gvJaime/microspot/Mechanical/Step/Printed/Axes/YCarriage/LYCarriage.step

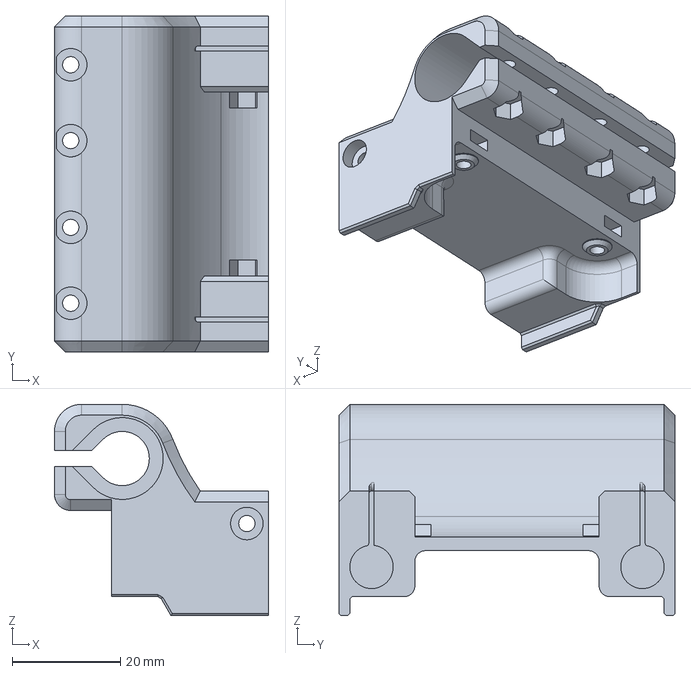
[picture p22: CAD file, 2017-04-26]
Mechanical/Step/Printed/Axes/YCarriage/LYCarriage.step
39.5 x 62.0 x 39.0 mm
