gvJaime/microspot/Mechanical/Step/Printed/Axes/ZAxis/BackCraneGuide.step

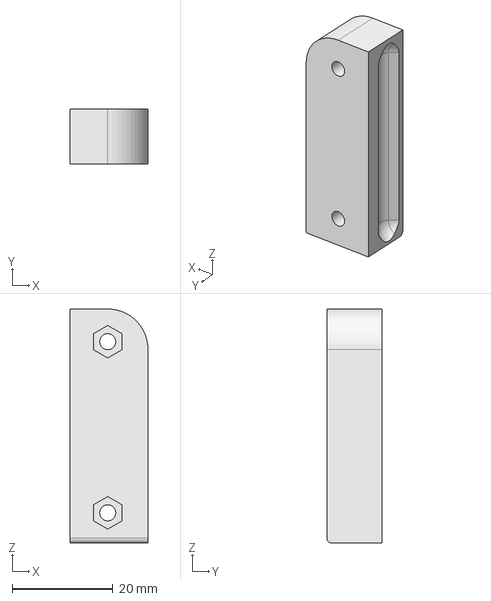
[picture p23: CAD file, 2018-11-02]
Mechanical/Step/Printed/Axes/ZAxis/BackCraneGuide.step
15.5 x 11.0 x 46.5 mm
