gvJaime/microspot/Mechanical/Step/Printed/Electronics Holder/ElecBase.step

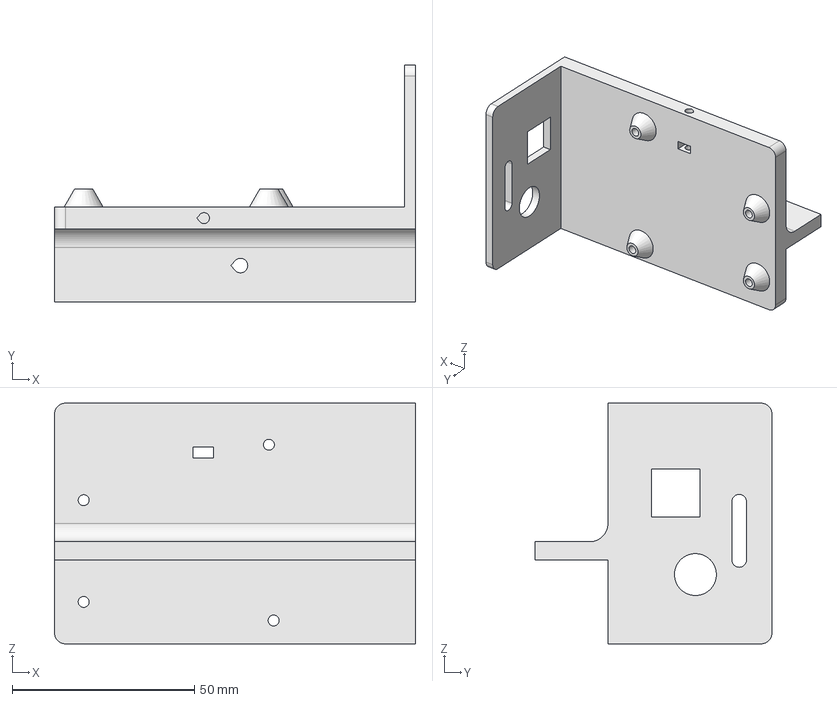
[picture p24: CAD file, 2016-09-07]
Mechanical/Step/Printed/Electronics Holder/ElecBase.step
99.0 x 65.0 x 66.0 mm
