gvJaime/microspot/Mechanical/Step/Printed/MainFrame/LAxisShield.step

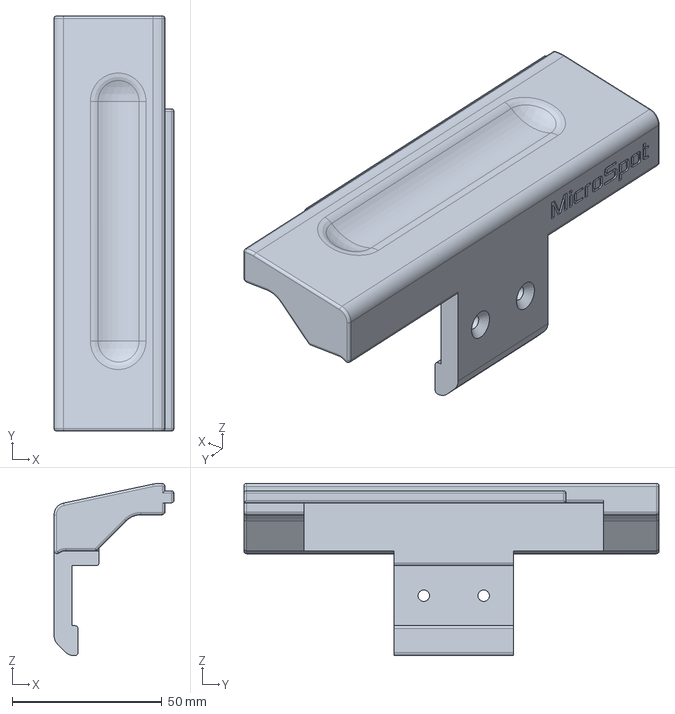
[picture p25: CAD file, 2018-11-02]
Mechanical/Step/Printed/MainFrame/LAxisShield.step
40.0 x 138.5 x 57.5 mm
