gvJaime/microspot/Mechanical/Step/Printed/PhoneHolder/Ratchet.step

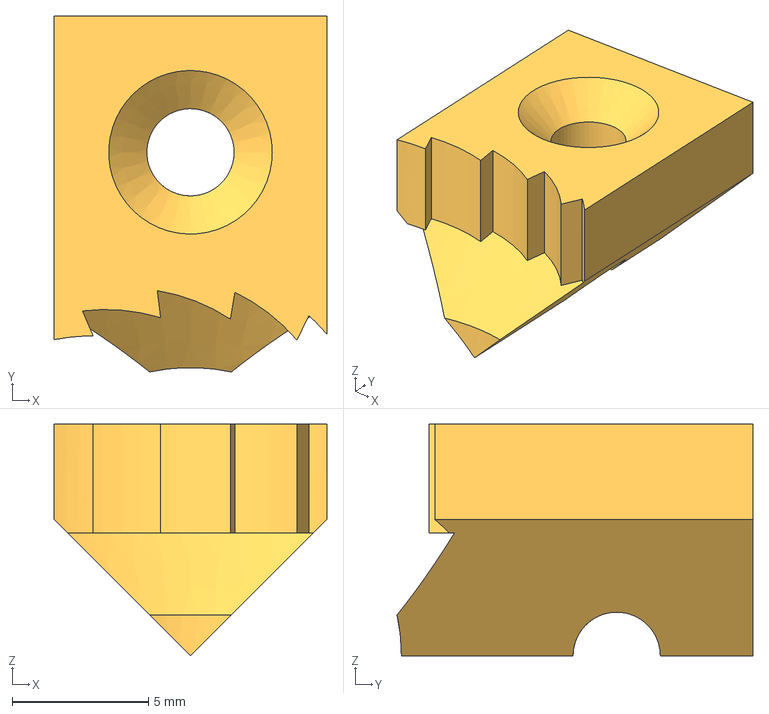
[picture p26: CAD file, 2018-11-02]
Mechanical/Step/Printed/PhoneHolder/Ratchet.step
10.0 x 13.1 x 8.50 mm
