gvJaime/microspot/Mechanical/Step/Printed/SmartphoneHolder/LPhoneGrip.step

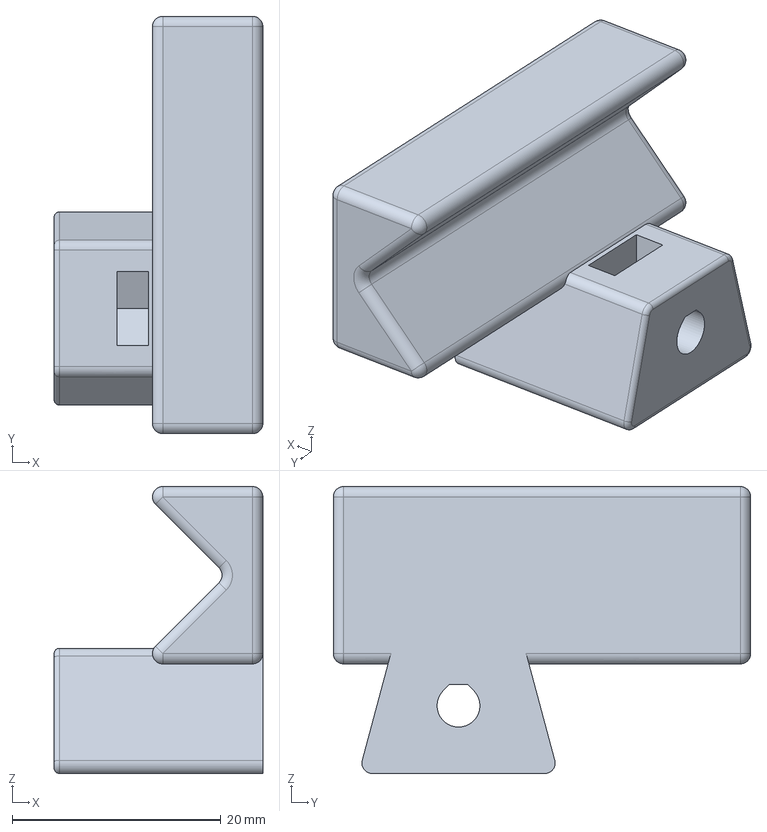
[picture p27: CAD file, 2017-04-26]
Mechanical/Step/Printed/SmartphoneHolder/LPhoneGrip.step
20.0 x 40.0 x 27.5 mm
