gvJaime/microspot/Optical/KO_LA0704/Lid.step

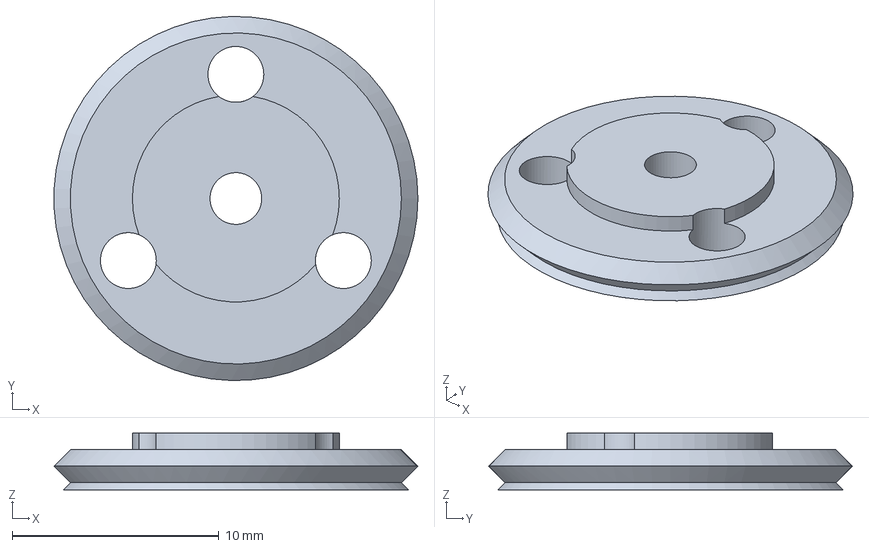
[picture p28: CAD file, 2018-11-02]
Optical/KO_LA0704/Lid.step
17.6 x 17.6 x 2.75 mm
