gvJaime/microspot/Optical/KO_LAQ0202nLAP0617/Lower.step

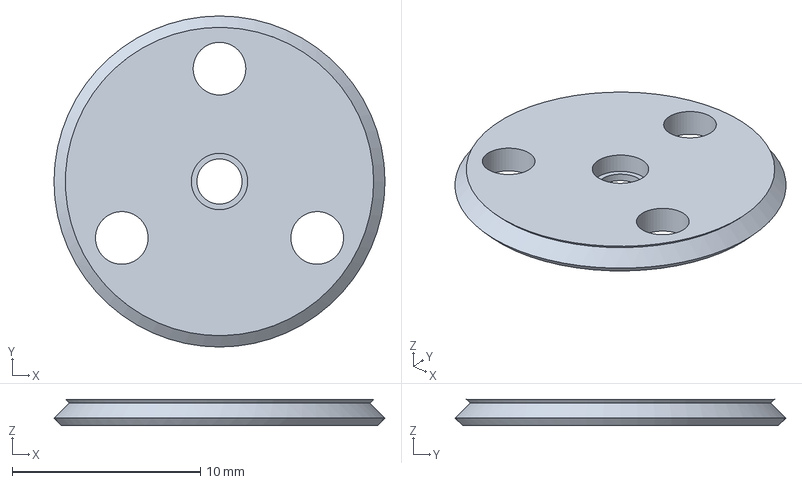
[picture p29: CAD file, 2018-11-02]
Optical/KO_LAQ0202nLAP0617/Lower.step
17.6 x 17.6 x 1.40 mm
