gvJaime/microspot/Optical/LensMount/LensFixTemplate.fcstd

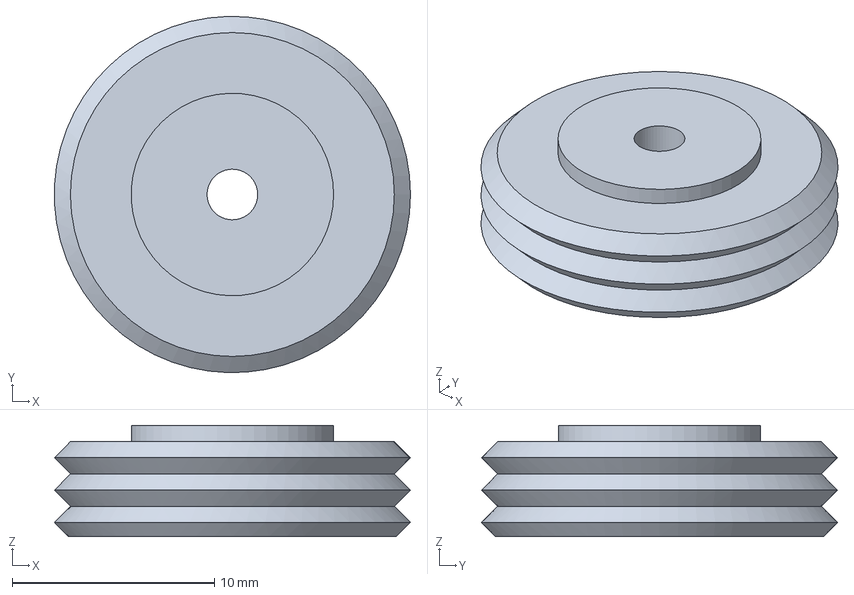
[picture p30: CAD file, 2018-11-02]
Optical/LensMount/LensFixTemplate.fcstd
17.6 x 17.6 x 5.50 mm
