gvJaime/microspot/Tools/NEMAChanger.fcstd

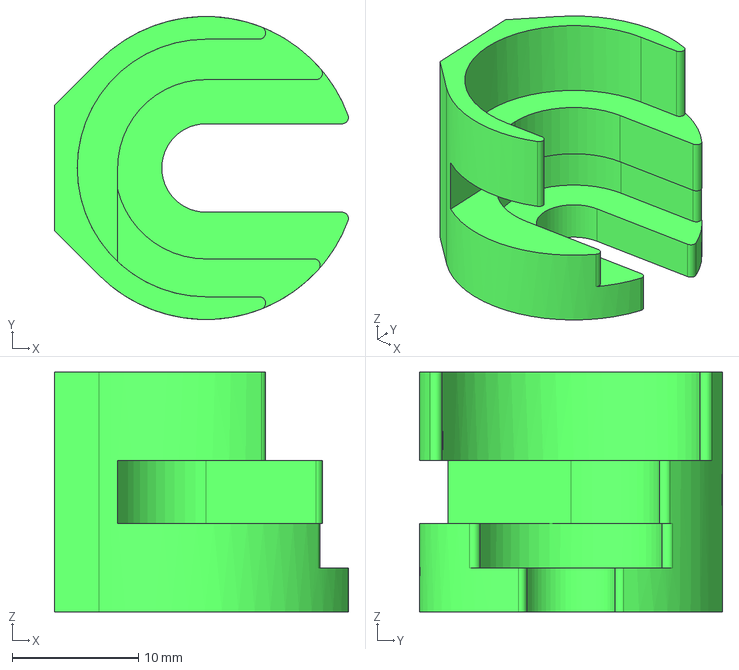
[picture p31: CAD file, 2018-11-02]
Tools/NEMAChanger.fcstd
23.3 x 24.0 x 19.0 mm
