gvJaime/microspot/Mechanical/src/Axes/XCarriage/FastRead102/FastReadFix.fcstd

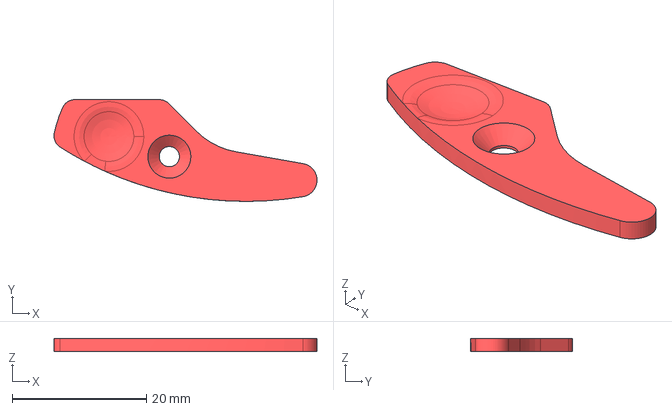
[picture p32: CAD file, 2017-07-26]
Mechanical/src/Axes/XCarriage/FastRead102/FastReadFix.fcstd
39.2 x 15.2 x 2.00 mm
