gvJaime/microspot/Mechanical/src/Axes/XCarriage/Neubauer/NeubauerTop.fcstd

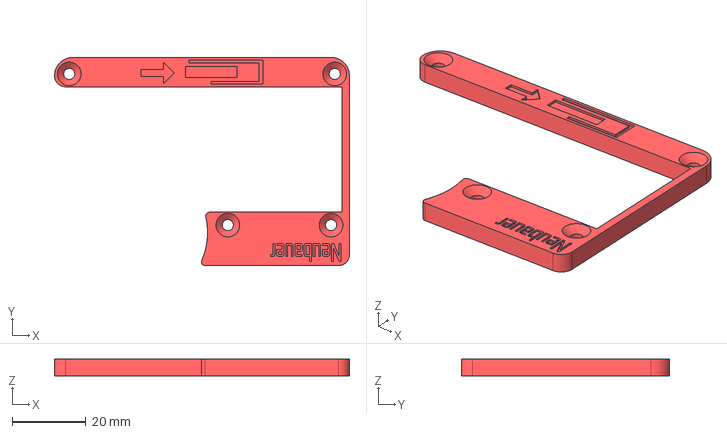
[picture p33: CAD file, 2018-11-02]
Mechanical/src/Axes/XCarriage/Neubauer/NeubauerTop.fcstd
80.0 x 56.5 x 4.50 mm
