gvJaime/microspot/Mechanical/src/Axes/XCarriage/StdTray/StdTop.fcstd

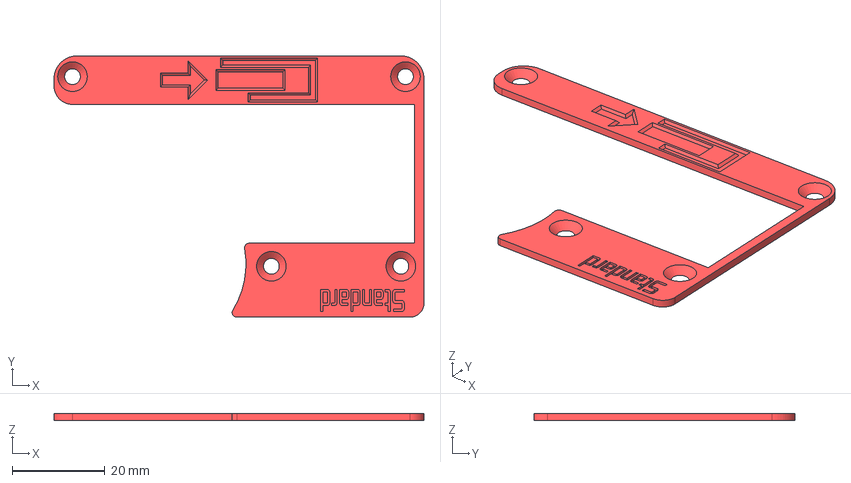
[picture p34: CAD file, 2018-11-02]
Mechanical/src/Axes/XCarriage/StdTray/StdTop.fcstd
80.0 x 56.5 x 1.50 mm
