gvJaime/microspot/Mechanical/src/Axes/XCarriage/Xcarriage.fcstd

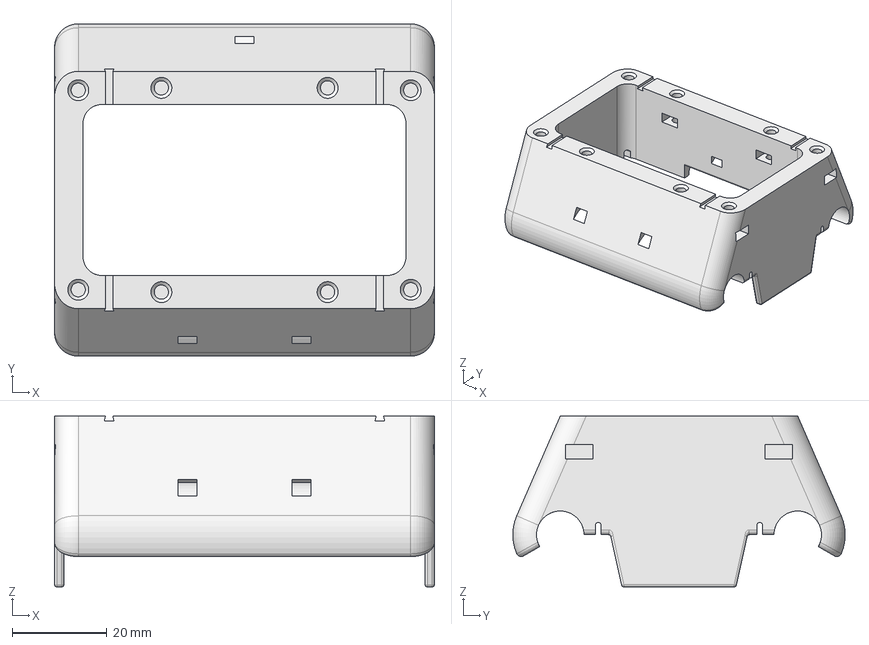
[picture p35: CAD file, 2016-09-07]
Mechanical/src/Axes/XCarriage/Xcarriage.fcstd
80.0 x 70.0 x 36.0 mm
