gvJaime/microspot/Mechanical/src/Axes/YCarriage/MiniIdler.fcstd

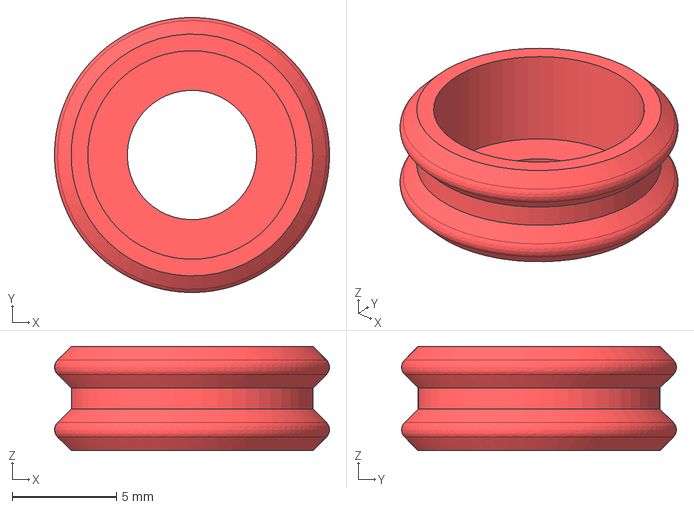
[picture p36: CAD file, 2016-04-19]
Mechanical/src/Axes/YCarriage/MiniIdler.fcstd
13.2 x 13.2 x 5.00 mm
