gvJaime/microspot/Mechanical/src/Axes/ZCarriage/FrontGuide.fcstd

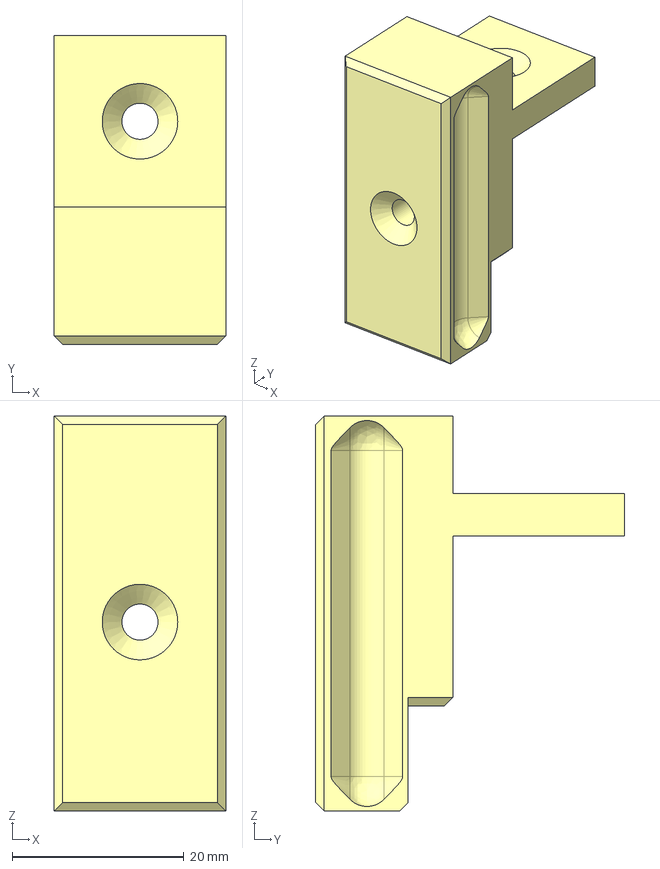
[picture p37: CAD file, 2018-11-02]
Mechanical/src/Axes/ZCarriage/FrontGuide.fcstd
20.0 x 36.0 x 46.0 mm
