gvJaime/microspot/Mechanical/src/MainFrame/FrontCorner.fcstd

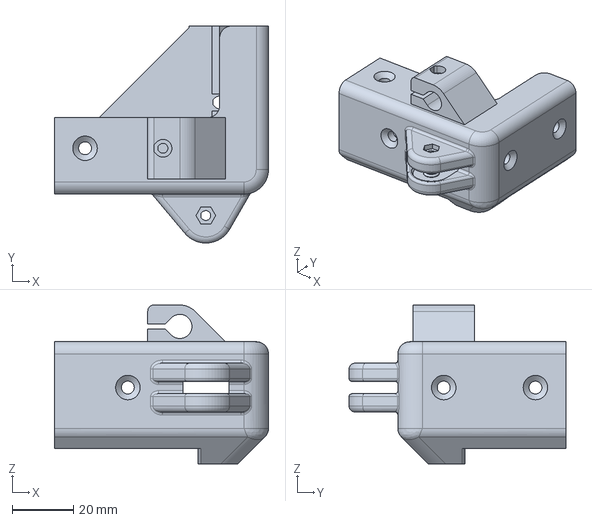
[picture p38: CAD file, 2018-11-02]
Mechanical/src/MainFrame/FrontCorner.fcstd
70.0 x 71.0 x 52.0 mm
