gvJaime/microspot/Mechanical/src/MainFrame/Reference/ALULED.fcstd

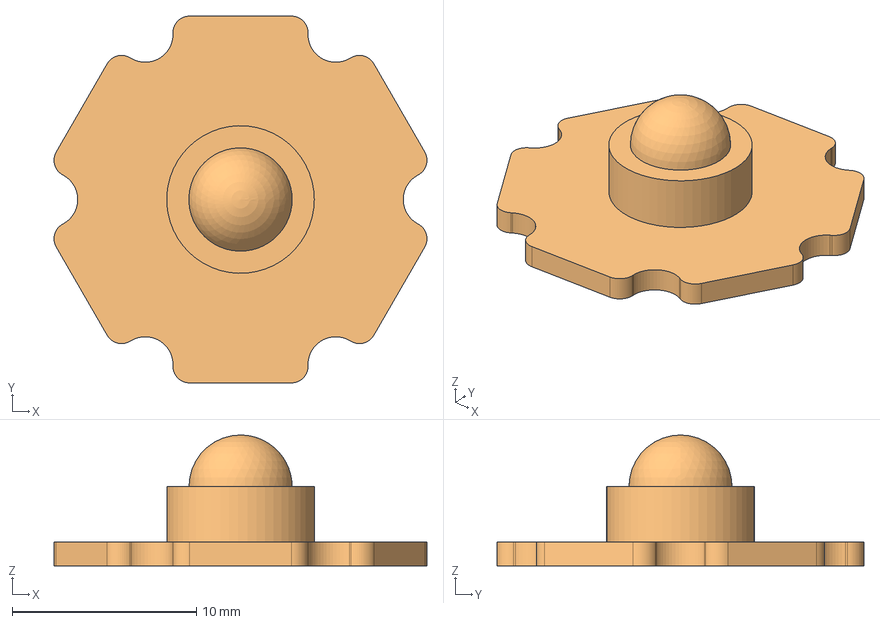
[picture p39: CAD file, 2016-09-07]
Mechanical/src/MainFrame/Reference/ALULED.fcstd
20.2 x 19.9 x 7.10 mm
LEDballFusion
ALULED
