gvJaime/microspot/Mechanical/src/UpperLid/UpperCover.fcstd

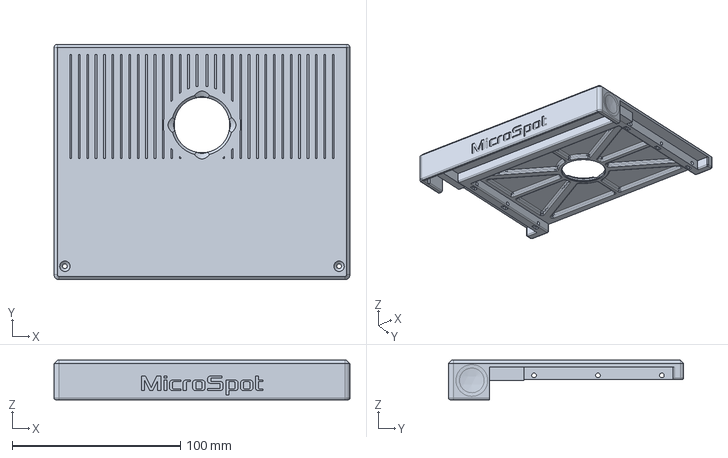
[picture p40: CAD file, 2018-11-02]
Mechanical/src/UpperLid/UpperCover.fcstd
176.0 x 140.0 x 23.5 mm
