gvJaime/microspot/Mechanical/Step/Components/4018X SNGL.stp

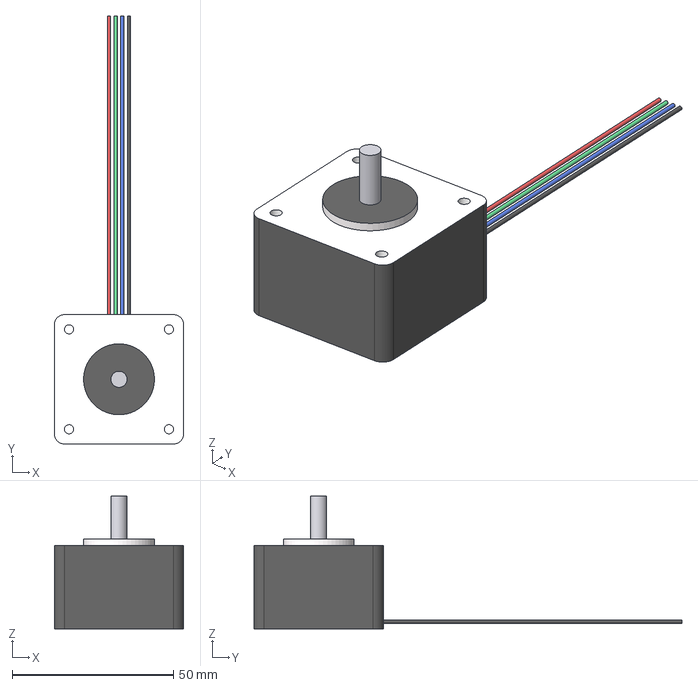
[picture p41: CAD file, 2015-11-04]
Mechanical/Step/Components/4018X SNGL.stp
40.1 x 132.8 x 41.1 mm
