gvJaime/microspot/Mechanical/Step/Printed/Axes/ZAxis/FrontCraneGuide.step

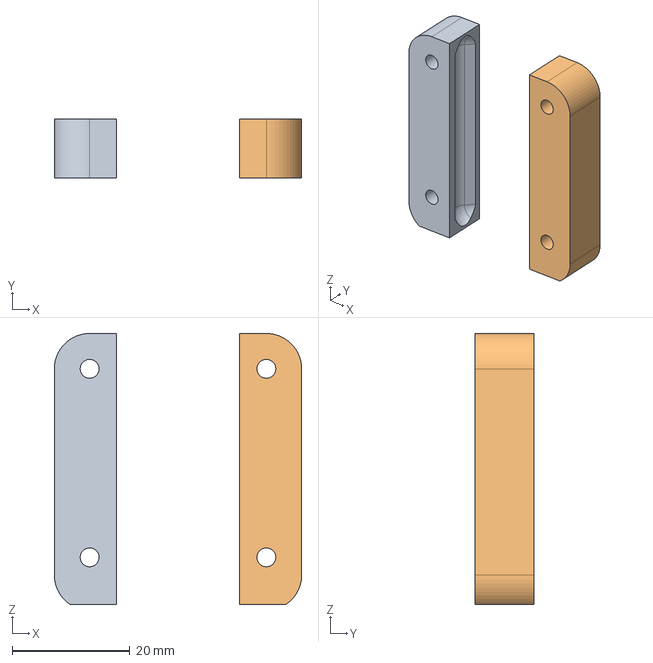
[picture p42: CAD file, 2018-11-02]
Mechanical/Step/Printed/Axes/ZAxis/FrontCraneGuide.step
42.0 x 10.0 x 46.0 mm
