gvJaime/microspot/Mechanical/Step/Printed/Electronics Holder/Lid.step

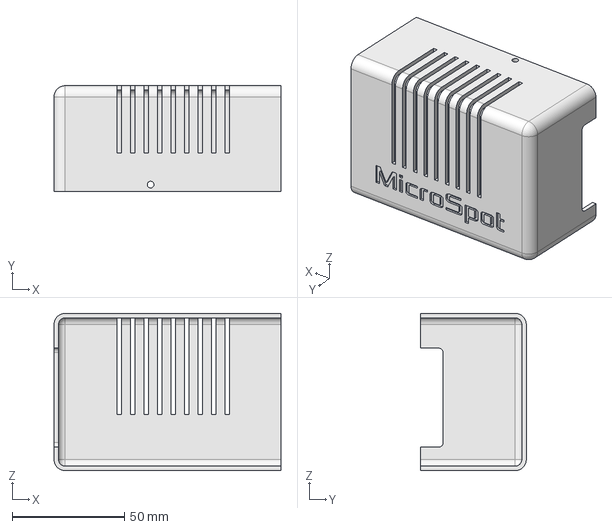
[picture p43: CAD file, 2016-09-07]
Mechanical/Step/Printed/Electronics Holder/Lid.step
101.0 x 47.0 x 70.0 mm
