gvJaime/microspot/Mechanical/Step/Printed/MainFrame/LBackCorner.step

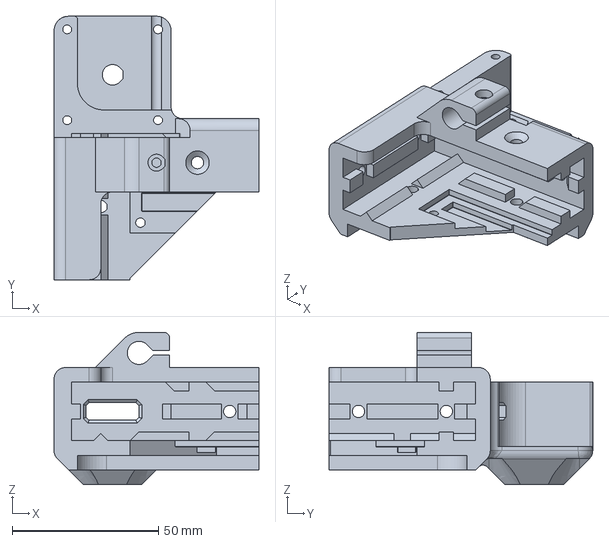
[picture p44: CAD file, 2018-11-02]
Mechanical/Step/Printed/MainFrame/LBackCorner.step
70.0 x 90.0 x 52.0 mm
