gvJaime/microspot/Mechanical/Step/Printed/SmartphoneHolder/LowerPhoneCarriage.step

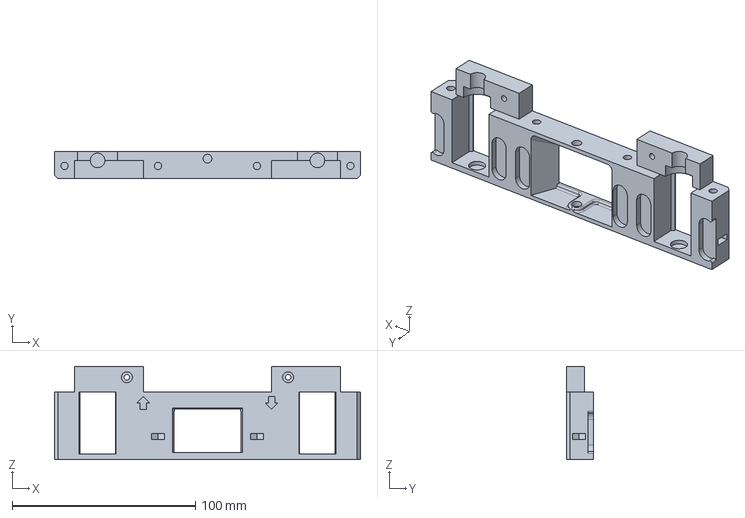
[picture p45: CAD file, 2017-04-26]
Mechanical/Step/Printed/SmartphoneHolder/LowerPhoneCarriage.step
167.0 x 15.0 x 51.0 mm
