gvJaime/microspot/Optical/KO_LA0704/KO_LA0704.fcstd

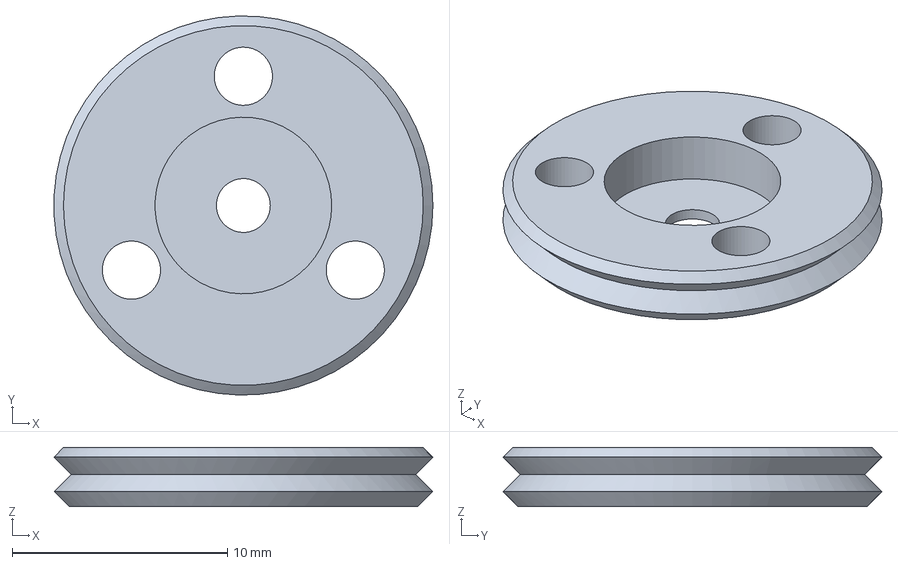
[picture p46: CAD file, 2018-11-02]
Optical/KO_LA0704/KO_LA0704.fcstd
17.6 x 17.6 x 2.75 mm
