gvJaime/microspot/Optical/KO_LAQ0202nLAP0617/LAQ0202nLAP0617.fcstd

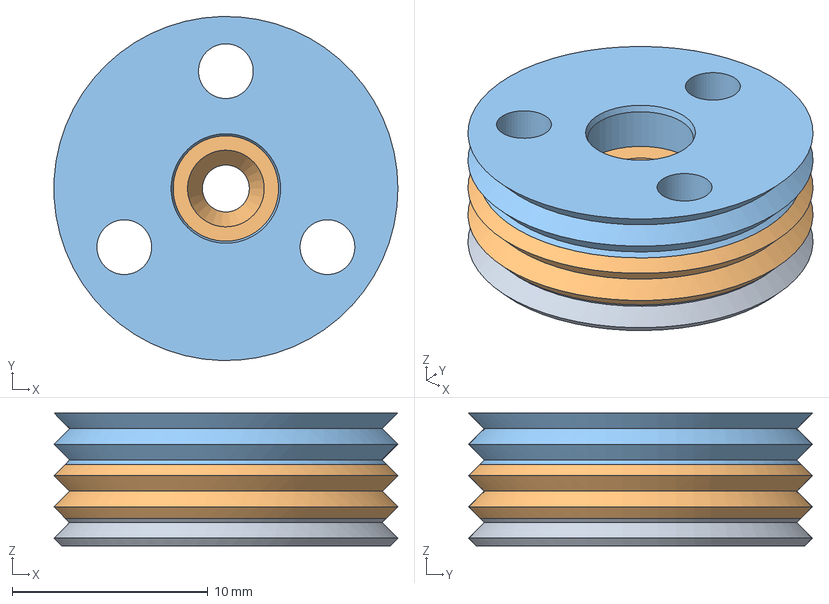
[picture p47: CAD file, 2018-11-02]
Optical/KO_LAQ0202nLAP0617/LAQ0202nLAP0617.fcstd
17.6 x 17.6 x 6.80 mm
LAQ0202nLAQ0617Lower
LAQ0202nLAQ0617Middle
LAQ0202nLAQ0617Upper
