gvJaime/microspot/Optical/LensMount/FlexiRing.fcstd

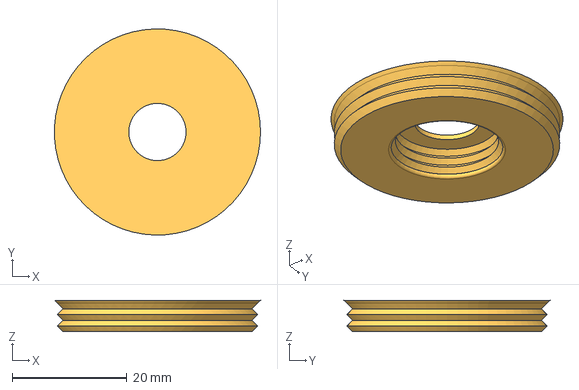
[picture p48: CAD file, 2018-11-02]
Optical/LensMount/FlexiRing.fcstd
36.0 x 36.0 x 5.50 mm
