gvJaime/microspot/Mechanical/src/Axes/XCarriage/Neubauer/NeubauerFix.fcstd

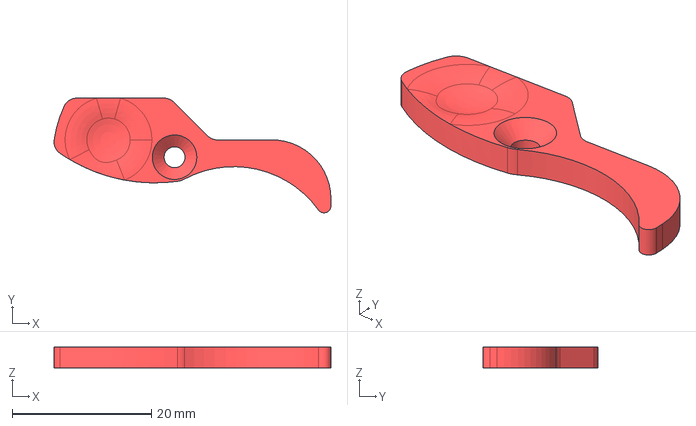
[picture p49: CAD file, 2017-07-26]
Mechanical/src/Axes/XCarriage/Neubauer/NeubauerFix.fcstd
39.8 x 16.5 x 3.00 mm
