gvJaime/microspot/Mechanical/src/Axes/XCarriage/StdTray/StdFix.fcstd

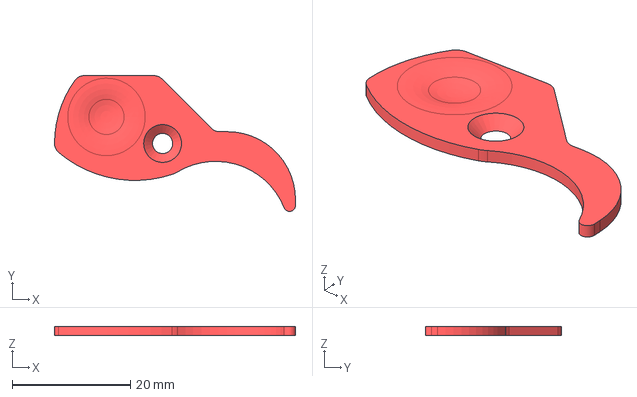
[picture p50: CAD file, 2017-07-19]
Mechanical/src/Axes/XCarriage/StdTray/StdFix.fcstd
40.8 x 23.0 x 1.50 mm
