gvJaime/microspot/Mechanical/src/Axes/ZCarriage/DrawerGuide.fcstd

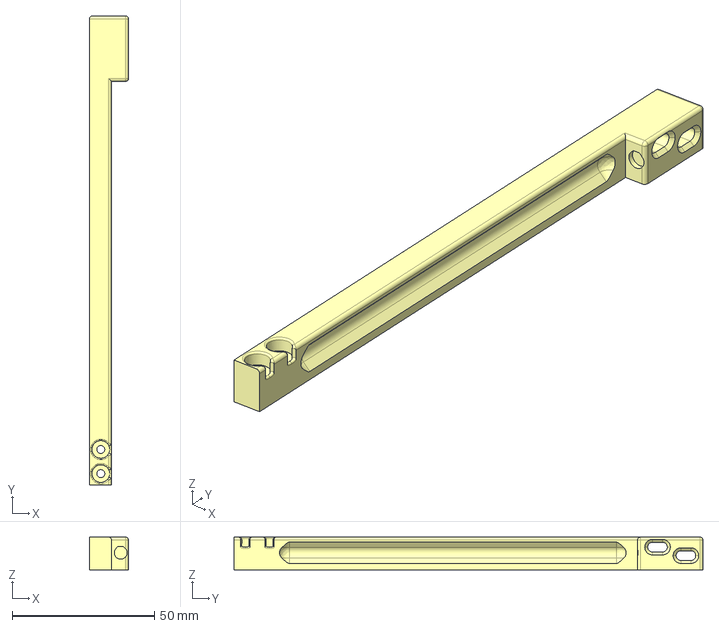
[picture p51: CAD file, 2018-11-02]
Mechanical/src/Axes/ZCarriage/DrawerGuide.fcstd
13.8 x 165.0 x 11.5 mm
