gvJaime/microspot/Mechanical/src/Electronics Holder/DummySwitch.fcstd

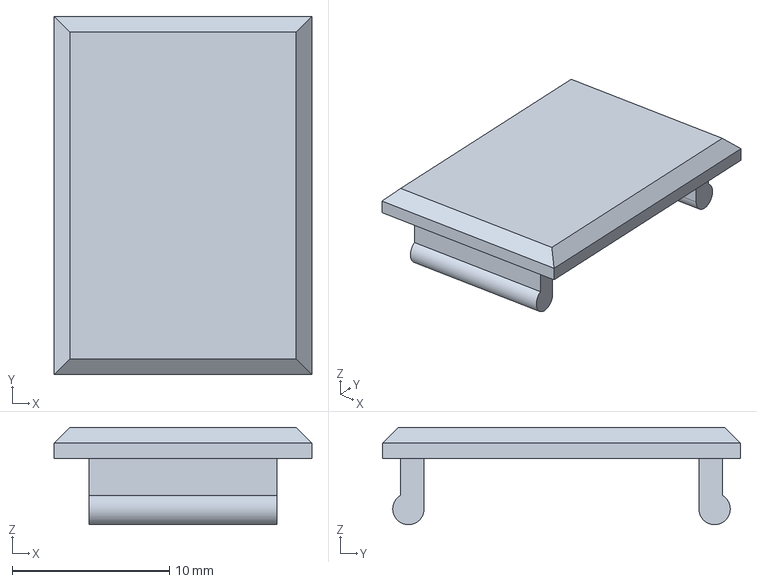
[picture p52: CAD file, 2017-07-19]
Mechanical/src/Electronics Holder/DummySwitch.fcstd
16.4 x 22.8 x 6.20 mm
