gvJaime/microspot/Mechanical/src/MainFrame/LowerCover.fcstd

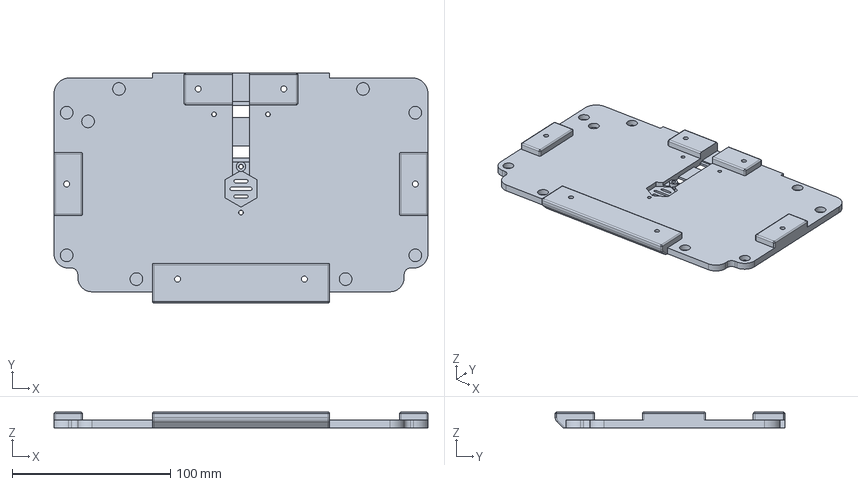
[picture p53: CAD file, 2018-11-02]
Mechanical/src/MainFrame/LowerCover.fcstd
236.0 x 145.0 x 10.0 mm
