gvJaime/microspot/Mechanical/Step/Components/NEMA8x13.step

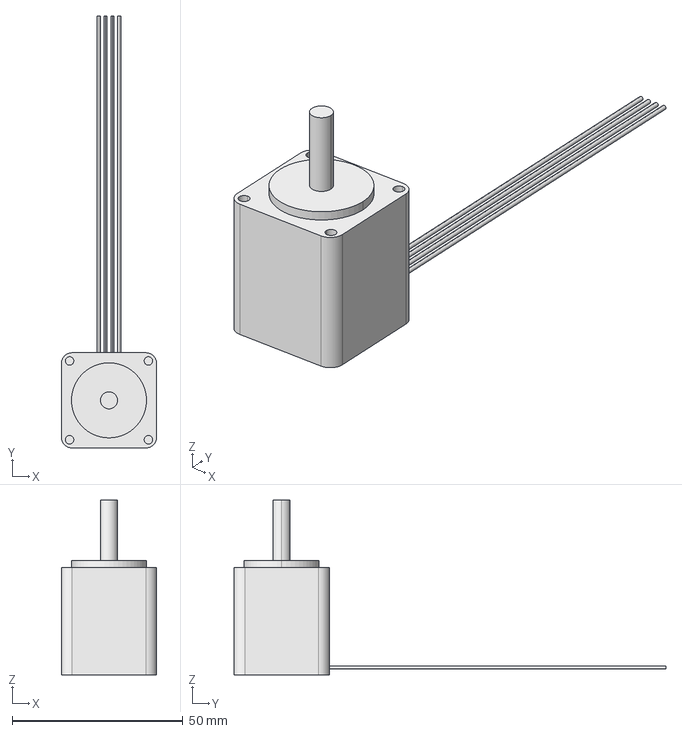
[picture p54: CAD file, 2015-11-04]
Mechanical/Step/Components/NEMA8x13.step
27.9 x 126.7 x 51.3 mm
