gvJaime/microspot/Mechanical/Step/Printed/MainFrame/TubeLid.step

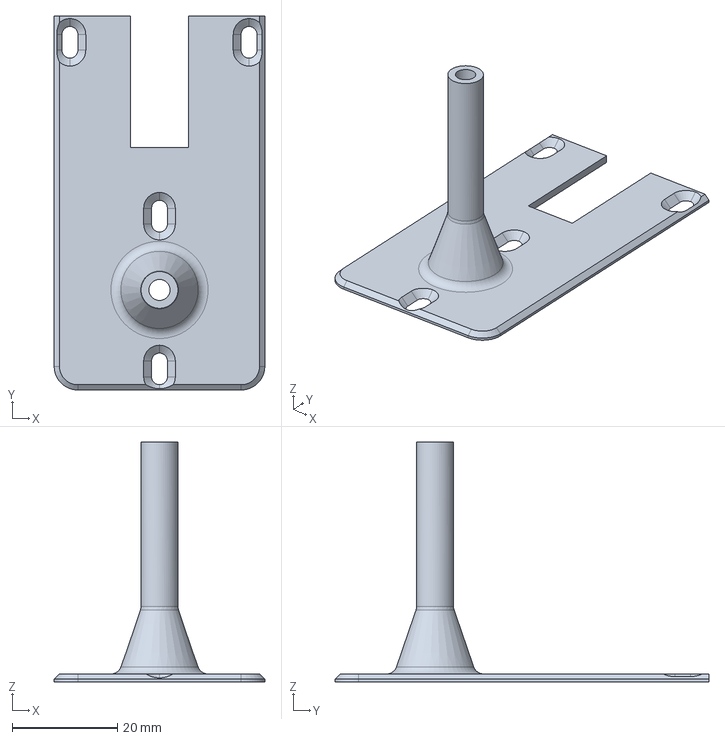
[picture p55: CAD file, 2018-11-02]
Mechanical/Step/Printed/MainFrame/TubeLid.step
40.0 x 71.0 x 45.5 mm
