gvJaime/microspot/Optical/KO_LAQ0202nLAP0617/Middle.step

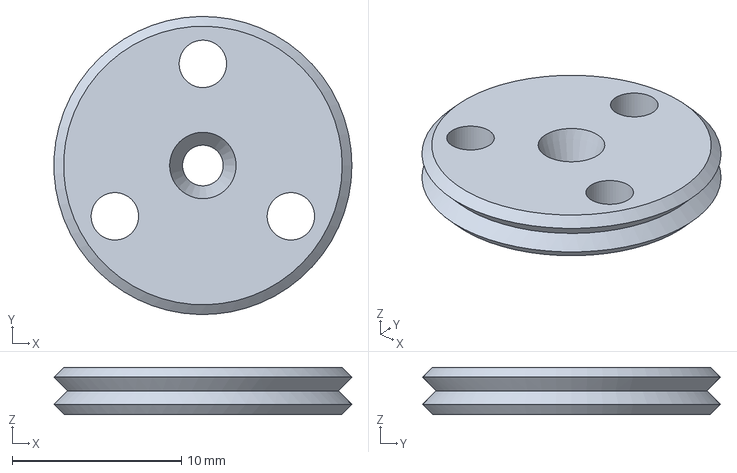
[picture p56: CAD file, 2018-11-02]
Optical/KO_LAQ0202nLAP0617/Middle.step
17.6 x 17.6 x 2.78 mm
