gvJaime/microspot/Mechanical/src/Axes/ZCarriage/FrontCrane.fcstd

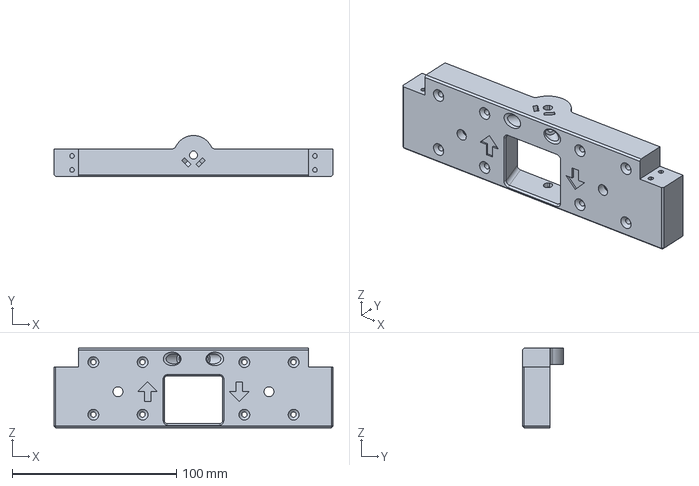
[picture p57: CAD file, 2018-11-02]
Mechanical/src/Axes/ZCarriage/FrontCrane.fcstd
170.0 x 25.0 x 48.5 mm
