gvJaime/microspot/Mechanical/src/MainFrame/PulleyCover.fcstd

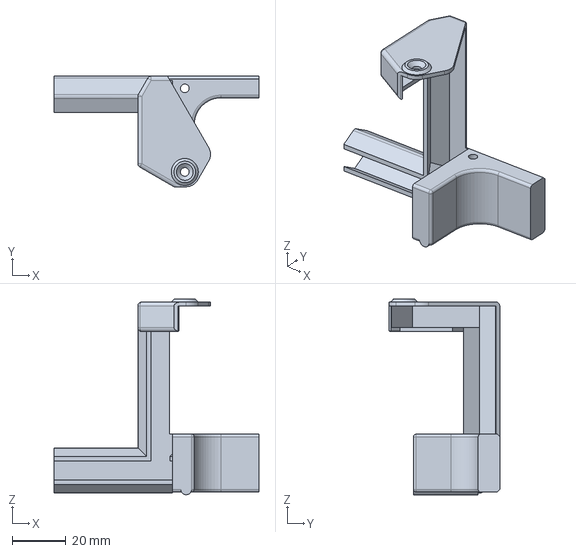
[picture p58: CAD file, 2018-11-02]
Mechanical/src/MainFrame/PulleyCover.fcstd
76.0 x 41.0 x 72.5 mm
