gvJaime/microspot/Mechanical/Step/Printed/SmartphoneHolder/UpperPhoneCarriage.step

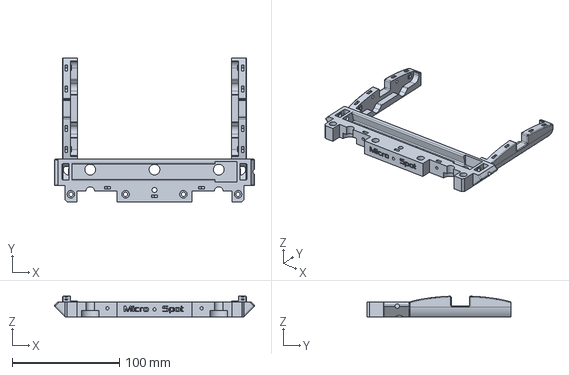
[picture p59: CAD file, 2017-04-26]
Mechanical/Step/Printed/SmartphoneHolder/UpperPhoneCarriage.step
186.7 x 134.0 x 19.3 mm
