gvJaime/microspot/Optical/KO_LA0704/Adaptor.fcstd

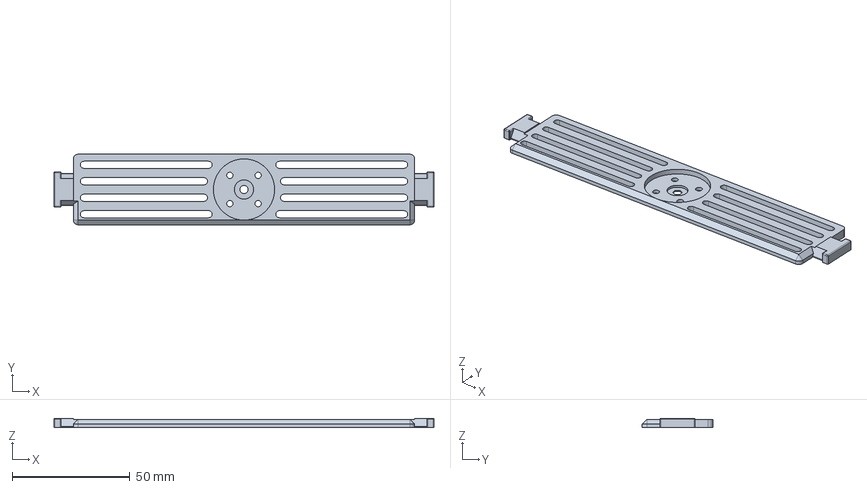
[picture p60: CAD file, 2018-03-20]
Optical/KO_LA0704/Adaptor.fcstd
161.4 x 30.0 x 4.00 mm
