gvJaime/microspot/Optical/KO_LAQ0202nLAP0617/FlexiRing.fcstd

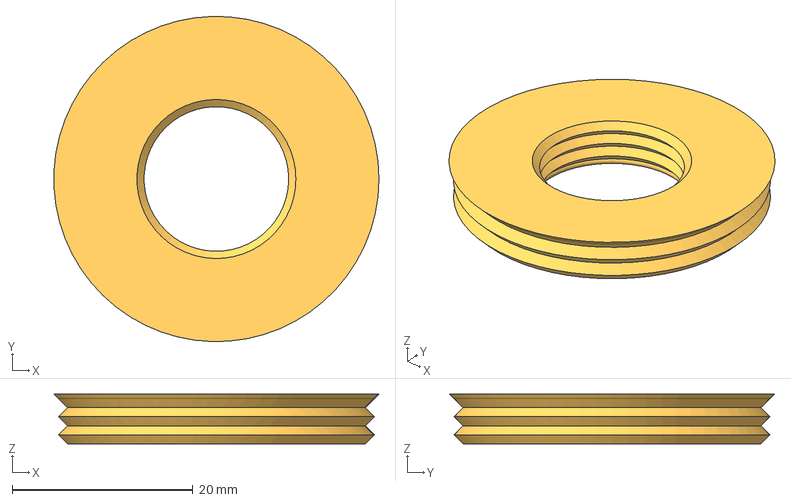
[picture p61: CAD file, 2018-11-02]
Optical/KO_LAQ0202nLAP0617/FlexiRing.fcstd
36.0 x 36.0 x 5.50 mm
