gvJaime/microspot/Mechanical/src/Axes/ZCarriage/FocusWheelHolder.fcstd

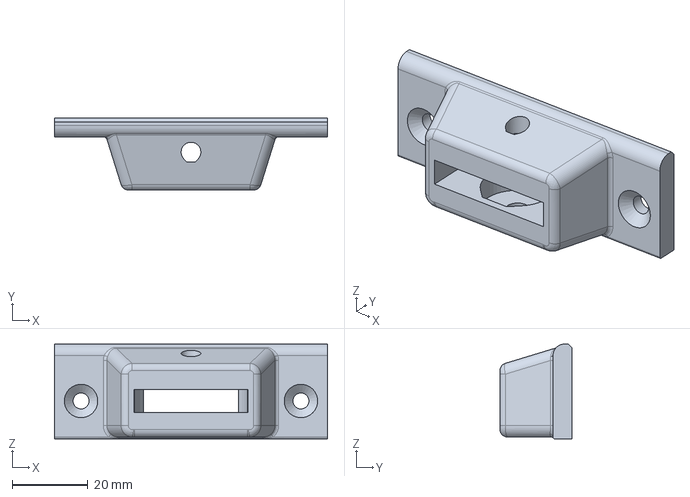
[picture p62: CAD file, 2018-11-02]
Mechanical/src/Axes/ZCarriage/FocusWheelHolder.fcstd
72.0 x 19.0 x 25.0 mm
