gvJaime/microspot/Optical/KO_LAQ0202nLAP0617/Upper.step

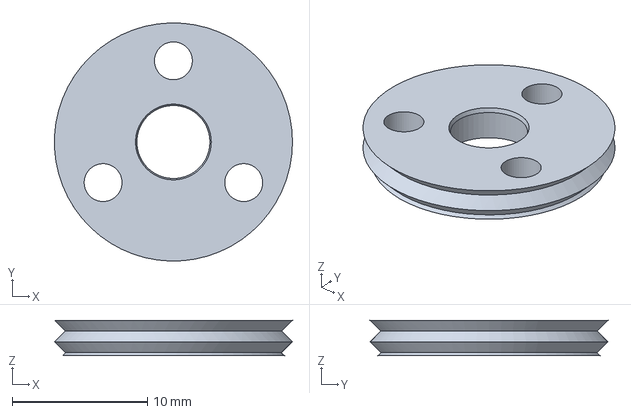
[picture p63: CAD file, 2018-11-02]
Optical/KO_LAQ0202nLAP0617/Upper.step
17.6 x 17.6 x 2.62 mm
