gvJaime/microspot/Mechanical/src/Axes/ZCarriage/UpperBackCover.fcstd

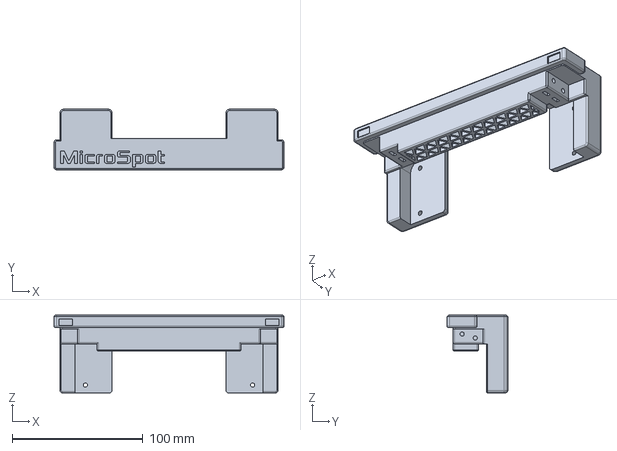
[picture p64: CAD file, 2018-11-02]
Mechanical/src/Axes/ZCarriage/UpperBackCover.fcstd
176.0 x 46.5 x 59.5 mm
