gvJaime/microspot/Mechanical/src/MainFrame/FrontIdler.fcstd

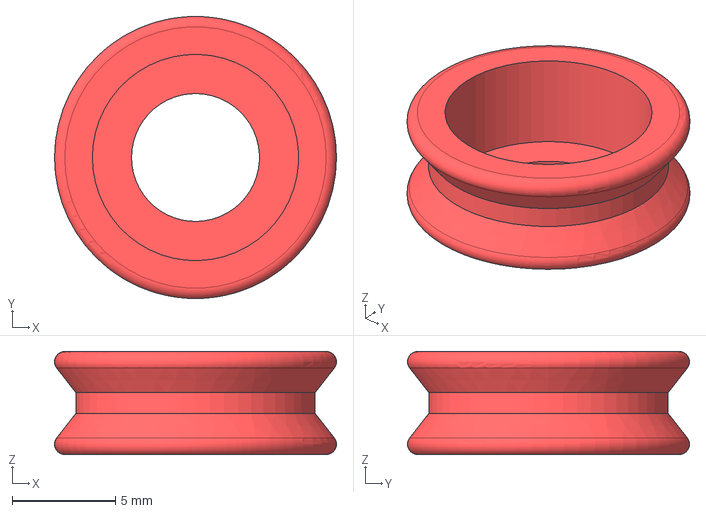
[picture p65: CAD file, 2016-09-07]
Mechanical/src/MainFrame/FrontIdler.fcstd
13.7 x 13.7 x 5.00 mm
